KyrianBunel/3D-printed-LoRa-weather-station/3D files/top cover v1.stl

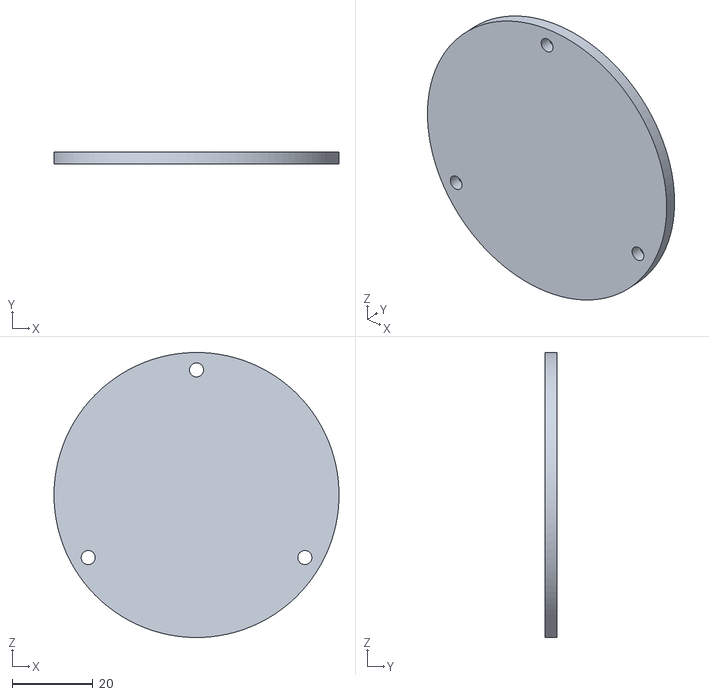
[picture p15: CAD file, 2024-12-03]
3D files/top cover v1.stl
70.8 x 3.00 x 70.8
